sp3esu/lights_controller/src/controller/ui.cpp

#include "ui.h"
#include "ui_icons.h"
#include "espnow_tx.h"
#include "display.h"
#include "protocol.h"
#include <lvgl.h>

// Color definitions
#define COLOR_BG        lv_color_hex(0x0F0F1A)

// ON colors per light
#define COLOR_FOG_ON     lv_color_hex(0xFFB84D)  // amber
#define COLOR_LOW_ON     lv_color_hex(0x44DD44)  // green
#define COLOR_HIGH_ON    lv_color_hex(0x4488FF)  // blue
#define COLOR_BAR_ON     lv_color_hex(0xFFFFFF)  // white
#define COLOR_HAZARD_ON  lv_color_hex(0xFF4444)  // red
#define COLOR_SETTINGS   lv_color_hex(0x888888)  // gray (settings button)

// Number of light buttons (excludes settings)
#define NUM_LIGHTS 5
// Total buttons including settings
#define NUM_BUTTONS 6
// Settings button index
#define IDX_SETTINGS 5
// Light button indices
#define IDX_LOW_BEAM  0
#define IDX_HIGH_BEAM 3
// Disabled icon color
#define COLOR_DISABLED lv_color_hex(0x333333)

// Light button info
struct LightBtnInfo {
    uint8_t            light_bit;
    const lv_img_dsc_t *icon;
    lv_color_t         on_color;
};

static const LightBtnInfo btn_info[NUM_BUTTONS] = {
    { LIGHT_LOW_BEAM,  &icon_low_beam,  COLOR_LOW_ON },     // [0] swapped
    { LIGHT_FOG,       &icon_fog,       COLOR_FOG_ON },     // [1] swapped
    { LIGHT_HAZARD,    &icon_hazard,    COLOR_HAZARD_ON },  // [2] new
    { LIGHT_HIGH_BEAM, &icon_high_beam, COLOR_HIGH_ON },    // [3]
    { LIGHT_BAR,       &icon_light_bar, COLOR_BAR_ON },     // [4]
    { 0,               &icon_settings,  COLOR_SETTINGS },   // [5] settings (not a light)
};

// UI elements
static lv_obj_t *scr_main = nullptr;
static lv_obj_t *scr_pairing = nullptr;
static lv_obj_t *scr_settings = nullptr;
static lv_obj_t *btn_objs[NUM_BUTTONS] = {};
static lv_obj_t *btn_icons[NUM_BUTTONS] = {};

static bool updating_ui = false;  // guard against recursive events
static bool test_mode = false;    // local-only toggle without ESP-NOW

static void apply_btn_style(int idx, bool on) {
    lv_obj_t *btn = btn_objs[idx];
    if (on) {
        // ON: colored background, dark icon
        lv_obj_set_style_bg_opa(btn, LV_OPA_COVER, LV_PART_MAIN);
        lv_obj_set_style_bg_color(btn, btn_info[idx].on_color, LV_PART_MAIN);
        lv_obj_set_style_img_recolor(btn_icons[idx], COLOR_BG, LV_PART_MAIN);
    } else {
        // OFF: transparent background, colored icon
        lv_obj_set_style_bg_opa(btn, LV_OPA_TRANSP, LV_PART_MAIN);
        lv_obj_set_style_img_recolor(btn_icons[idx], btn_info[idx].on_color, LV_PART_MAIN);
    }
    lv_obj_set_style_img_recolor_opa(btn_icons[idx], LV_OPA_COVER, LV_PART_MAIN);

    if (on) lv_obj_add_state(btn, LV_STATE_CHECKED);
    else    lv_obj_clear_state(btn, LV_STATE_CHECKED);
}

static void update_high_beam_enabled() {
    bool low_on = lv_obj_has_state(btn_objs[IDX_LOW_BEAM], LV_STATE_CHECKED);
    lv_obj_t *hb_btn = btn_objs[IDX_HIGH_BEAM];
    lv_obj_t *hb_icon = btn_icons[IDX_HIGH_BEAM];

    if (!low_on) {
        // Disable high beam: not clickable, dark gray icon, force OFF
        lv_obj_clear_flag(hb_btn, LV_OBJ_FLAG_CLICKABLE);
        lv_obj_clear_state(hb_btn, LV_STATE_CHECKED);
        lv_obj_set_style_bg_opa(hb_btn, LV_OPA_TRANSP, LV_PART_MAIN);
        lv_obj_set_style_img_recolor(hb_icon, COLOR_DISABLED, LV_PART_MAIN);
    } else {
        // Enable high beam: restore clickable, restore color for current state
        lv_obj_add_flag(hb_btn, LV_OBJ_FLAG_CLICKABLE);
        bool hb_on = lv_obj_has_state(hb_btn, LV_STATE_CHECKED);
        if (hb_on) {
            lv_obj_set_style_img_recolor(hb_icon, COLOR_BG, LV_PART_MAIN);
        } else {
            lv_obj_set_style_img_recolor(hb_icon, btn_info[IDX_HIGH_BEAM].on_color, LV_PART_MAIN);
        }
    }
}

static void btn_event_cb(lv_event_t *e) {
    if (updating_ui) return;

    lv_obj_t *btn = lv_event_get_target(e);
    int idx = (int)(intptr_t)lv_event_get_user_data(e);
    bool checked = lv_obj_has_state(btn, LV_STATE_CHECKED);

    // Block high beam if low beam is off
    if (idx == IDX_HIGH_BEAM && !lv_obj_has_state(btn_objs[IDX_LOW_BEAM], LV_STATE_CHECKED)) {
        lv_obj_clear_state(btn, LV_STATE_CHECKED);
        apply_btn_style(idx, false);
        return;
    }

    // Optimistic UI update
    apply_btn_style(idx, checked);

    // In test mode, just toggle locally; otherwise send via ESP-NOW
    if (!test_mode) {
        espnow_tx_toggle_light(btn_info[idx].light_bit);
    }

    // Low beam toggled OFF → also turn off high beam
    if (idx == IDX_LOW_BEAM && !checked) {
        if (lv_obj_has_state(btn_objs[IDX_HIGH_BEAM], LV_STATE_CHECKED)) {
            apply_btn_style(IDX_HIGH_BEAM, false);
            if (!test_mode) {
                espnow_tx_send_state(LIGHT_HIGH_BEAM, 0);
            }
        }
    }

    // Update high beam enabled/disabled state after any low beam change
    if (idx == IDX_LOW_BEAM) {
        update_high_beam_enabled();
    }
}

static void settings_btn_event_cb(lv_event_t *e) {
    (void)e;
    ui_show_settings();
}

static void settings_pairing_cb(lv_event_t *e) {
    (void)e;
    espnow_tx_start_pairing();
    ui_show_pairing();
}

static void settings_back_cb(lv_event_t *e) {
    (void)e;
    lv_scr_load(scr_main);
}

static lv_obj_t *create_light_button(lv_obj_t *parent, int idx) {
    lv_obj_t *btn = lv_obj_create(parent);
    lv_obj_remove_style_all(btn);
    lv_obj_set_size(btn, 101, 80);
    lv_obj_set_style_bg_opa(btn, LV_OPA_TRANSP, LV_PART_MAIN);
    lv_obj_set_style_radius(btn, 12, LV_PART_MAIN);

    // Checkable toggle
    lv_obj_add_flag(btn, LV_OBJ_FLAG_CHECKABLE | LV_OBJ_FLAG_CLICKABLE);

    // Pressed feedback: semi-transparent white overlay (works for both ON and OFF)
    lv_obj_set_style_bg_opa(btn, LV_OPA_30, (lv_style_selector_t)(LV_PART_MAIN | LV_STATE_PRESSED));
    lv_obj_set_style_bg_color(btn, lv_color_white(), (lv_style_selector_t)(LV_PART_MAIN | LV_STATE_PRESSED));

    // Center content
    lv_obj_set_flex_flow(btn, LV_FLEX_FLOW_COLUMN);
    lv_obj_set_flex_align(btn, LV_FLEX_ALIGN_CENTER, LV_FLEX_ALIGN_CENTER, LV_FLEX_ALIGN_CENTER);

    // Icon — starts with light's signature color (OFF state)
    lv_obj_t *img = lv_img_create(btn);
    lv_img_set_src(img, btn_info[idx].icon);
    lv_obj_set_style_img_recolor(img, btn_info[idx].on_color, LV_PART_MAIN);
    lv_obj_set_style_img_recolor_opa(img, LV_OPA_COVER, LV_PART_MAIN);
    lv_obj_clear_flag(img, LV_OBJ_FLAG_CLICKABLE);
    btn_icons[idx] = img;

    // Event
    lv_obj_add_event_cb(btn, btn_event_cb, LV_EVENT_VALUE_CHANGED, (void *)(intptr_t)idx);

    btn_objs[idx] = btn;
    return btn;
}

static lv_obj_t *create_settings_button(lv_obj_t *parent) {
    int idx = IDX_SETTINGS;
    lv_obj_t *btn = lv_obj_create(parent);
    lv_obj_remove_style_all(btn);
    lv_obj_set_size(btn, 101, 80);
    lv_obj_set_style_bg_opa(btn, LV_OPA_TRANSP, LV_PART_MAIN);
    lv_obj_set_style_radius(btn, 12, LV_PART_MAIN);

    // Clickable only (not checkable)
    lv_obj_add_flag(btn, LV_OBJ_FLAG_CLICKABLE);

    // Pressed feedback
    lv_obj_set_style_bg_opa(btn, LV_OPA_30, (lv_style_selector_t)(LV_PART_MAIN | LV_STATE_PRESSED));
    lv_obj_set_style_bg_color(btn, lv_color_white(), (lv_style_selector_t)(LV_PART_MAIN | LV_STATE_PRESSED));

    // Center content
    lv_obj_set_flex_flow(btn, LV_FLEX_FLOW_COLUMN);
    lv_obj_set_flex_align(btn, LV_FLEX_ALIGN_CENTER, LV_FLEX_ALIGN_CENTER, LV_FLEX_ALIGN_CENTER);

    // Icon — fixed gray color
    lv_obj_t *img = lv_img_create(btn);
    lv_img_set_src(img, btn_info[idx].icon);
    lv_obj_set_style_img_recolor(img, COLOR_SETTINGS, LV_PART_MAIN);
    lv_obj_set_style_img_recolor_opa(img, LV_OPA_COVER, LV_PART_MAIN);
    lv_obj_clear_flag(img, LV_OBJ_FLAG_CLICKABLE);
    btn_icons[idx] = img;

    // Event — opens settings screen
    lv_obj_add_event_cb(btn, settings_btn_event_cb, LV_EVENT_CLICKED, nullptr);

    btn_objs[idx] = btn;
    return btn;
}

static lv_obj_t *create_settings_menu_btn(lv_obj_t *parent, const char *text, lv_event_cb_t cb) {
    lv_obj_t *btn = lv_obj_create(parent);
    lv_obj_remove_style_all(btn);
    lv_obj_set_size(btn, 280, 50);
    lv_obj_set_style_bg_color(btn, lv_color_hex(0x2A2A3A), LV_PART_MAIN);
    lv_obj_set_style_bg_opa(btn, LV_OPA_COVER, LV_PART_MAIN);
    lv_obj_set_style_radius(btn, 10, LV_PART_MAIN);
    lv_obj_add_flag(btn, LV_OBJ_FLAG_CLICKABLE);

    // Pressed feedback
    lv_obj_set_style_bg_color(btn, lv_color_hex(0x4A4A5A), (lv_style_selector_t)(LV_PART_MAIN | LV_STATE_PRESSED));

    // Center the label
    lv_obj_set_flex_flow(btn, LV_FLEX_FLOW_COLUMN);
    lv_obj_set_flex_align(btn, LV_FLEX_ALIGN_CENTER, LV_FLEX_ALIGN_CENTER, LV_FLEX_ALIGN_CENTER);

    lv_obj_t *label = lv_label_create(btn);
    lv_label_set_text(label, text);
    lv_obj_set_style_text_color(label, lv_color_white(), LV_PART_MAIN);
    lv_obj_set_style_text_font(label, &lv_font_montserrat_16, LV_PART_MAIN);
    lv_obj_clear_flag(label, LV_OBJ_FLAG_CLICKABLE);

    lv_obj_add_event_cb(btn, cb, LV_EVENT_CLICKED, nullptr);
    return btn;
}

void ui_init() {
    // Main screen
    scr_main = lv_obj_create(NULL);
    lv_obj_set_style_bg_color(scr_main, COLOR_BG, LV_PART_MAIN);
    lv_obj_set_style_bg_opa(scr_main, LV_OPA_COVER, LV_PART_MAIN);
    lv_obj_set_style_pad_all(scr_main, 0, LV_PART_MAIN);

    // Full-screen 2x3 grid
    lv_obj_t *grid = lv_obj_create(scr_main);
    lv_obj_remove_style_all(grid);
    lv_obj_set_size(grid, DISP_WIDTH, DISP_HEIGHT);
    lv_obj_align(grid, LV_ALIGN_TOP_LEFT, 0, 0);
    lv_obj_set_style_pad_all(grid, 4, LV_PART_MAIN);
    lv_obj_set_style_pad_gap(grid, 4, LV_PART_MAIN);
    lv_obj_clear_flag(grid, LV_OBJ_FLAG_SCROLLABLE);

    // 2x3 flex layout with wrap
    lv_obj_set_flex_flow(grid, LV_FLEX_FLOW_ROW_WRAP);
    lv_obj_set_flex_align(grid, LV_FLEX_ALIGN_SPACE_EVENLY, LV_FLEX_ALIGN_SPACE_EVENLY, LV_FLEX_ALIGN_SPACE_EVENLY);

    // Create 5 light buttons + 1 settings button
    for (int i = 0; i < NUM_LIGHTS; i++) {
        create_light_button(grid, i);
    }
    create_settings_button(grid);

    // High beam starts disabled (low beam is off)
    update_high_beam_enabled();

    // Pairing screen
    scr_pairing = lv_obj_create(NULL);
    lv_obj_set_style_bg_color(scr_pairing, COLOR_BG, LV_PART_MAIN);
    lv_obj_set_style_bg_opa(scr_pairing, LV_OPA_COVER, LV_PART_MAIN);

    lv_obj_t *pair_label = lv_label_create(scr_pairing);
    lv_label_set_text(pair_label, "Pairing...");
    lv_obj_set_style_text_color(pair_label, lv_color_white(), LV_PART_MAIN);
    lv_obj_set_style_text_font(pair_label, &lv_font_montserrat_16, LV_PART_MAIN);
    lv_obj_center(pair_label);

    lv_obj_t *spinner = lv_spinner_create(scr_pairing, 1000, 60);
    lv_obj_set_size(spinner, 50, 50);
    lv_obj_align(spinner, LV_ALIGN_CENTER, 0, 40);

    // Settings screen
    scr_settings = lv_obj_create(NULL);
    lv_obj_set_style_bg_color(scr_settings, COLOR_BG, LV_PART_MAIN);
    lv_obj_set_style_bg_opa(scr_settings, LV_OPA_COVER, LV_PART_MAIN);

    lv_obj_set_flex_flow(scr_settings, LV_FLEX_FLOW_COLUMN);
    lv_obj_set_flex_align(scr_settings, LV_FLEX_ALIGN_CENTER, LV_FLEX_ALIGN_CENTER, LV_FLEX_ALIGN_CENTER);
    lv_obj_set_style_pad_gap(scr_settings, 16, LV_PART_MAIN);

    create_settings_menu_btn(scr_settings, "Pairing", settings_pairing_cb);
    create_settings_menu_btn(scr_settings, "Back", settings_back_cb);
}

void ui_set_light_state(uint8_t state) {
    updating_ui = true;
    for (int i = 0; i < NUM_LIGHTS; i++) {
        bool on = (state & btn_info[i].light_bit) != 0;
        apply_btn_style(i, on);
    }
    update_high_beam_enabled();
    updating_ui = false;
}

void ui_set_connection_status(bool connected) {
    // Connection state shown via NeoPixel — no on-screen indicator
    (void)connected;
}

void ui_show_pairing() {
    lv_scr_load(scr_pairing);
}

void ui_show_main() {
    lv_scr_load(scr_main);
}

void ui_show_settings() {
    lv_scr_load(scr_settings);
}

void ui_set_test_mode(bool enabled) {
    test_mode = enabled;
}
