sp3esu/lights_controller/src/controller/ui_icons.cpp

#include "ui_icons.h"

// 48x48 pixel icons as LVGL-compatible alpha maps (LV_IMG_CF_ALPHA_8BIT)
// Each byte = one pixel alpha value (0x00 = transparent, 0xFF = opaque)
// Icons can be recolored via lv_obj_set_style_img_recolor()
// MDI icons: Apache 2.0 license, https://pictogrammers.com/library/mdi/

// Fog lamp icon (mdi:car-light-fog)
static const uint8_t fog_map[48 * 48] = {
      0,  0,  0,  0,  0,  0,  0,  0,  0,  0,  0,  0,  0,  0,  0,  0,  0,  0,  0,  0,  0,  0,  0,  0,  0,  0,  0,  0,  0,  0,  0,  0,  0,  0,  0,  0,  0,  0,  0,  0,  0,  0,  0,  0,  0,  0,  0,  0,
      0,  0,  0,  0,  0,  0,  0,  0,  0,  0,  0,  0,  0,  0,  0,  0,  0,  0,  0,  0,  0,  0,  0,  0,  0,  0,  0,  0,  0,  0,  0,  0,  0,  0,  0,  0,  0,  0,  0,  0,  0,  0,  0,  0,  0,  0,  0,  0,
      0,  0,  0,  0,  0,  0,  0,  0,  0,  0,  0,  0,  0,  0,  0,  0,  0,  0,  0,  0,  0,  0,  0,  0,  0,  0,  0,  0,  0,  0,  0,  0,  0,  0,  0,  0,  0,  0,  0,  0,  0,  0,  0,  0,  0,  0,  0,  0,
      0,  0,  0,  0,  0,  0,  0,  0,  0,  0,  0,  0,  0,  0,  0,  0,  0,  0,  0,  0,  0,  0,  0,  0,  0,  0,  0,  0,  0,  0,  0,  0,  0,  0,  0,  0,  0,  0,  0,  0,  0,  0,  0,  0,  0,  0,  0,  0,
      0,  0,  0,  0,  0,  0,  0,  0,  0,  0,  0,  0,  0,  0,  0,  0,  0,  0,  0,  0,  0,  0,  0,  0,  0,  0,  0,  0,  0,  0,  0,  0,  0,  0,  0,  0,  0,  0,  0,  0,  0,  0,  0,  0,  0,  0,  0,  0,
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
};

const lv_img_dsc_t icon_settings = {
    .header = {
        .cf = LV_IMG_CF_ALPHA_8BIT,
        .always_zero = 0,
        .reserved = 0,
        .w = 48,
        .h = 48,
    },
    .data_size = 48 * 48,
    .data = settings_map,
};
